dcuccia/digital-handbell/docs/measurements/2026-09-27-router-bakeoff/quilter-inferred/bypass_capacitors.csv

capacitor | bypassed_component | bypassed_pin | capacitance
C5 | U1 | 8 | 100
C9 | U2 | 5 | 100
C10 | U2 | 5 | 100
C11 | U2 | 5 | 100
C12 | U2 | 5 | 100
C13 | U2 | 5 | 100
C14 | U2 | 5 | 100
C15 | U2 | 5 | 100
C17 | U2 | 5 | 100
C23 | U2 | 5 | 100
C24 | U2 | 5 | 100
C26 | U5 | 3 | 22000
C27 | U4 | 7 | 22000
C28 | U4 | 8 | 22000
C2 | IC1 | 20 | 0.015
C3 | R6 | 1 | 0.015
C4 | U2 | 5 | 100
C6 | IC1 | 23 | 100
C7 | IC1 | 45 | 100
C8 | IC1 | 50 | 100
C21 | FB2 | 2 | 0.22
C22 | FB1 | 2 | 0.22
C1 | U2 | 1 | 100
C16 | U4 | 7 | 100
C18 | IC1 | 23 | 100
C19 | U4 | 7 | 100
C20 | CHG_EN0 | 2 | 100
C25 | IC1 | 30 | 10
