dcuccia/digital-handbell/hardware/handbell/iterations/printed-bell-front/reports/footprint-movements.csv

reference | from_native_xy_angle | to_native_xy_angle | from_side | to_side
C1 | [-5.819979, -12.535118, 180.0] | [-4.034775, -13.791182, 90] | F | F
C2 | [-7.491404, -0.208214, 90.0] | [-9.0964, -3.04755, 90] | F | F
C3 | [-7.491346, 1.914027, 270.0] | [-9.100819, -0.800669, 270] | F | F
C4 | [-13.404896, -5.309687, 0.0] | [-15.993581, -9.414015, 0] | F | F
C5 | [-11.417907, -10.812876, 180.0] | [-16.178591, -2.508548, 0] | F | F
C6 | [8.689622, -0.182451, 180.0] | [5.497898, -0.400256, 180] | F | F
C7 | [8.460429, 2.217699, 180.0] | [7.803336, 2.200014, 180] | F | F
C8 | [8.463329, 3.418004, 0.0] | [5.501069, 2.200145, 0] | F | F
C9 | [-5.765769, 3.036206, 180.0] | [2.615534, -5.271328, 90] | F | F
C10 | [3.059734, -7.563574, 180.0] | [5.294511, -6.217731, 90] | F | F
C11 | [-7.169298, 6.97243, 90.0] | [-0.994073, 5.195623, 270] | F | F
C12 | [3.059361, -6.228689, 180.0] | [-0.99995, -5.269923, 90] | F | F
C13 | [7.694268, 4.618099, 0.0] | [5.502546, 3.500537, 0] | F | F
C14 | [-2.832032, 1.442344, 180.0] | [-5.195705, 2.304504, 180] | F | F
C15 | [-2.408704, -1.416949, 90.0] | [2.589143, 5.196168, 270] | F | F
C16 | [10.584754, -15.261328, 0.0] | [11.33959, -6.983099, 0] | B | F
C17 | [8.390974, 1.017594, 0.0] | [5.499429, 0.897675, 0] | F | F
C18 | [-2.833131, 2.644313, 0.0] | [-5.19636, 1.003449, 0] | F | F
C19 | [7.434754, -15.811328, 0.0] | [14.218731, -6.93737, 0] | B | F
C20 | [-2.310305, 15.995891, 270.0] | [4.846036, -16.283889, 90] | F | F
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
U4 | [10.105463, -12.411328, 0.0] | [10.725323, -10.087789, 0] | B | F
U5 | [-1.168351, 15.064739, 90.0] | [-4.198999, 16.001796, 0] | B | F
U6 | [-11.496466, 7.350217, 0.0] | [-11.502673, 7.349061, 0] | F | F
Y1 | [-5.391298, 0.68593, 90.0] | [-6.925199, -1.997404, 90] | F | F
