dcuccia/digital-handbell/mechanical/studies/2026-09-13-printed-bell/imu-four-layer-review/extended-run/INERT-flush-carrier.stl

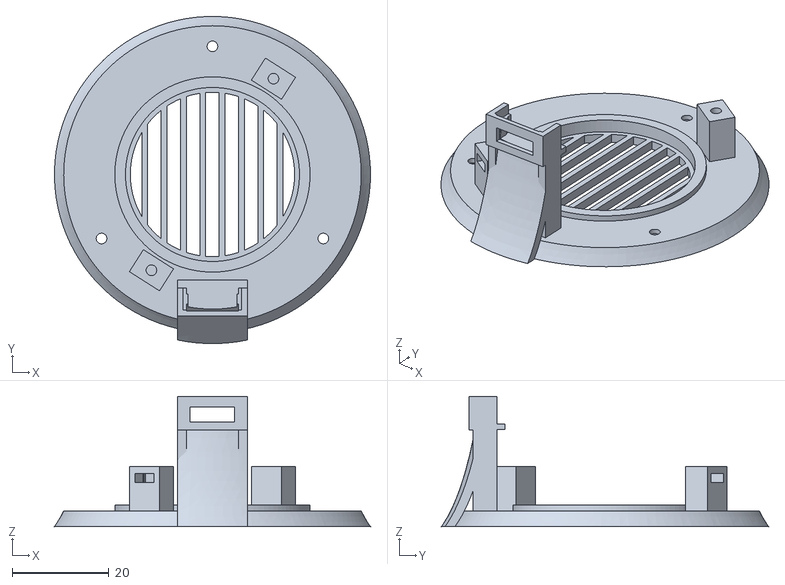
[picture p21: CAD file, 2026-09-24]
mechanical/studies/2026-09-13-printed-bell/imu-four-layer-review/extended-run/INERT-flush-carrier.stl
65.4 x 67.7 x 27.0
