dcuccia/digital-handbell/mechanical/grille.stl

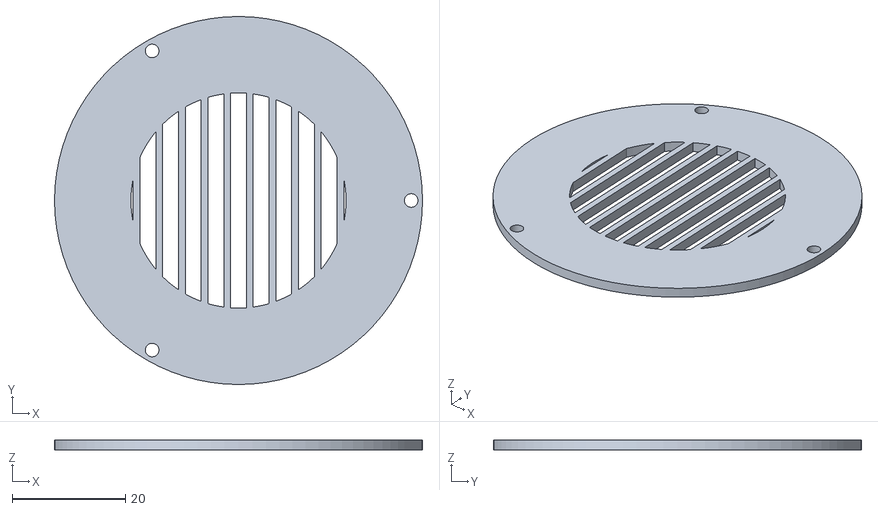
[picture p22: CAD file, 2026-09-07]
mechanical/grille.stl
65.0 x 65.0 x 1.80
