dcuccia/digital-handbell/mechanical/studies/2026-09-09-measured-speaker/outward-body-screen.step

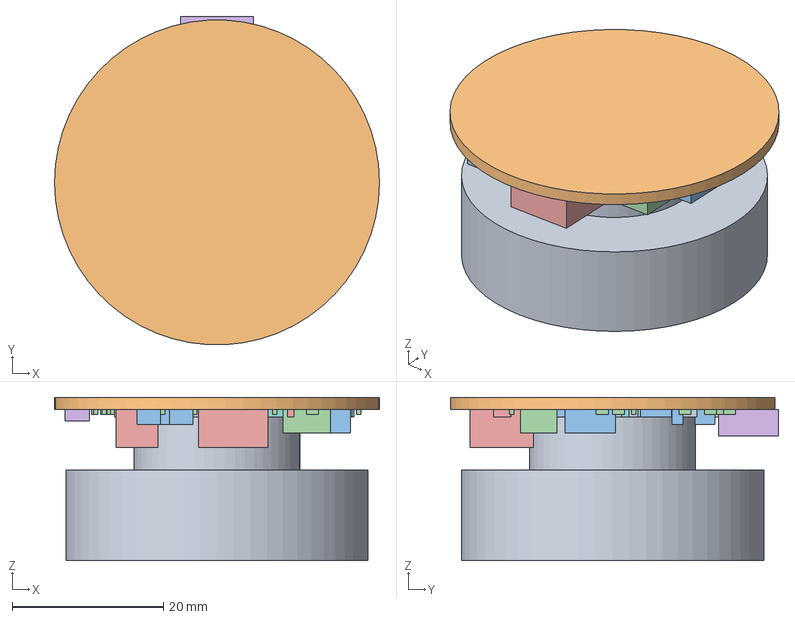
[picture p23: CAD file, 2026-09-09]
mechanical/studies/2026-09-09-measured-speaker/outward-body-screen.step
43.0 x 43.4 x 21.6 mm
