dcuccia/digital-handbell/mechanical/studies/2026-09-11-t8-cartridge/alternatives/baseline-fixed-stack/populated-t8-pcba-without-contacts.step

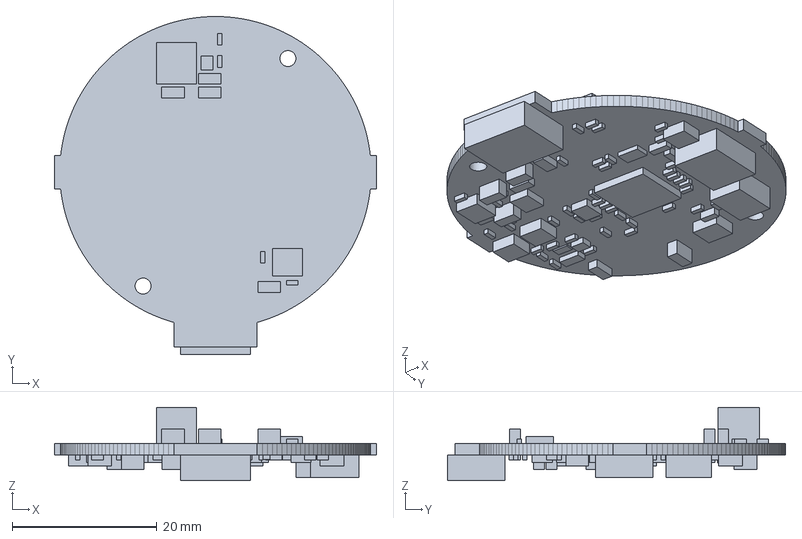
[picture p24: CAD file, 2026-09-12]
mechanical/studies/2026-09-11-t8-cartridge/alternatives/baseline-fixed-stack/populated-t8-pcba-without-contacts.step
44.5 x 46.6 x 10.1 mm
