dcuccia/digital-handbell/mechanical/speaker-envelope-maximum.stl

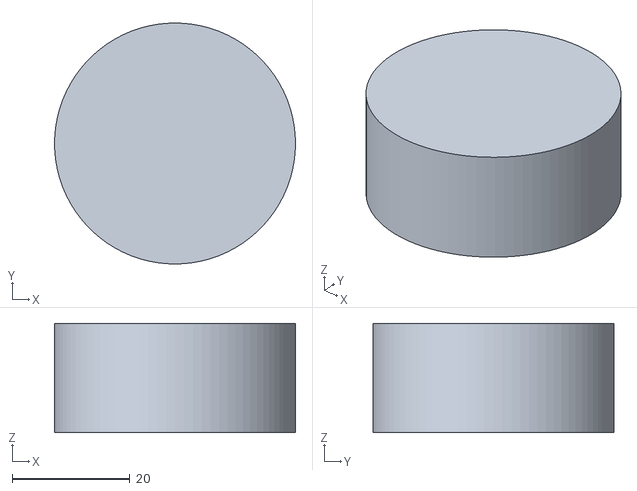
[picture p26: CAD file, 2026-09-07]
mechanical/speaker-envelope-maximum.stl
40.9 x 40.9 x 18.5
