dcuccia/digital-handbell/mechanical/studies/2026-09-09-integrated-cartridge/INERT-integrated-grille-seat-body.stl

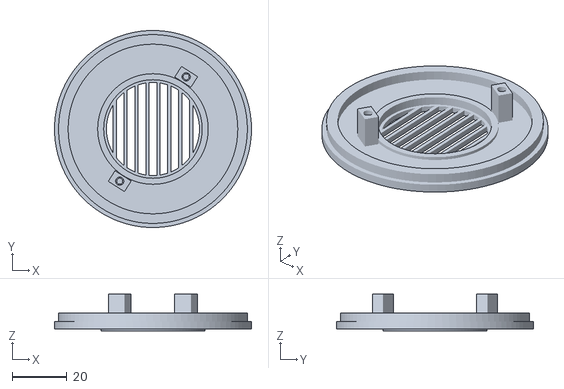
[picture p27: CAD file, 2026-09-10]
mechanical/studies/2026-09-09-integrated-cartridge/INERT-integrated-grille-seat-body.stl
72.0 x 72.0 x 13.5
