dcuccia/digital-handbell/mechanical/studies/2026-09-09-measured-speaker/measured-speaker-study.FCStd

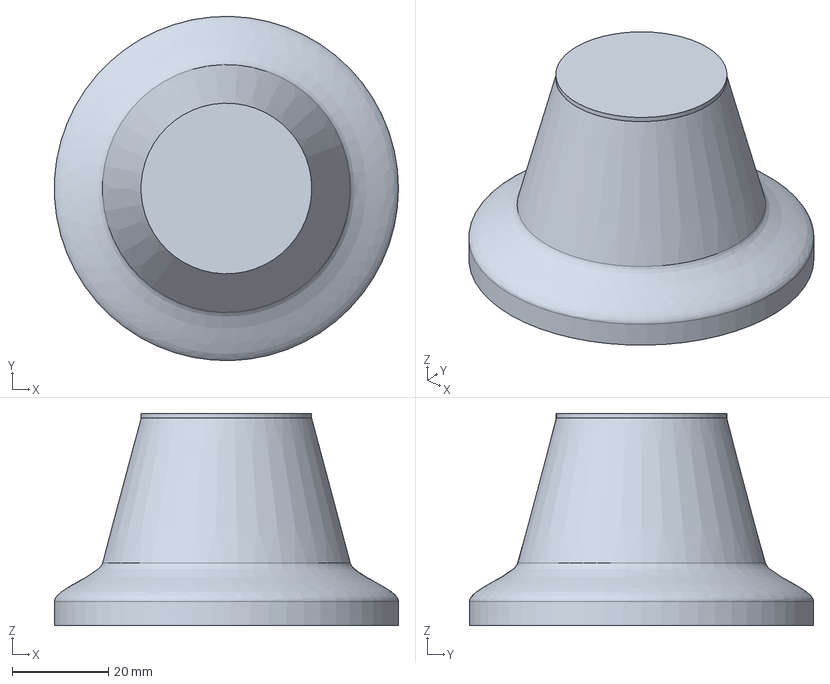
[picture p28: CAD file, 2026-09-09]
mechanical/studies/2026-09-09-measured-speaker/measured-speaker-study.FCStd
71.3 x 71.4 x 44.0 mm
ASSUMED shell; no USB slot; hide to inspect
ILLUSTRATIVE: straight basket interpolation
SCREEN: full measured D40 x H19 body cylinder
SCREEN: full-width basket + measured magnet
Unrouted substrate at z20
C1 - original unscaled component proxy
C2 - original unscaled component proxy
C3 - original unscaled component proxy
C4 - original unscaled component proxy
C5 - original unscaled component proxy
C6 - original unscaled component proxy
C7 - original unscaled component proxy
C8 - original unscaled component proxy
C9 - original unscaled component proxy
C10 - original unscaled component proxy
C11 - original unscaled component proxy
C12 - original unscaled component proxy
C13 - original unscaled component proxy
C14 - original unscaled component proxy
C15 - original unscaled component proxy
C16 - original unscaled component proxy
C17 - original unscaled component proxy
C18 - original unscaled component proxy
C19 - original unscaled component proxy
C20 - original unscaled component proxy
C21 - original unscaled component proxy
C22 - original unscaled component proxy
C23 - original unscaled component proxy
C24 - original unscaled component proxy
C25 - original unscaled component proxy
C26 - original unscaled component proxy
C27 - original unscaled component proxy
C28 - original unscaled component proxy
CHG0 - original unscaled component proxy
D3 - original unscaled component proxy
D4 - original unscaled component proxy
FB1 - original unscaled component proxy
FB2 - original unscaled component proxy
IC1 - original unscaled component proxy
IC4 - original unscaled component proxy
J1 - original unscaled component proxy
J2 - original unscaled component proxy
L0 - original unscaled component proxy
L1 - original unscaled component proxy
Q1 - original unscaled component proxy
Q2 - original unscaled component proxy
Q3 - original unscaled component proxy
Q4 - original unscaled component proxy
R1 - original unscaled component proxy
R2 - original unscaled component proxy
R3 - original unscaled component proxy
R4 - original unscaled component proxy
R5 - original unscaled component proxy
R6 - original unscaled component proxy
R7 - original unscaled component proxy
R8 - original unscaled component proxy
R9 - original unscaled component proxy
R10 - original unscaled component proxy
R11 - original unscaled component proxy
R12 - original unscaled component proxy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
