dcuccia/digital-handbell/mechanical/populated-pcba-proxy.step

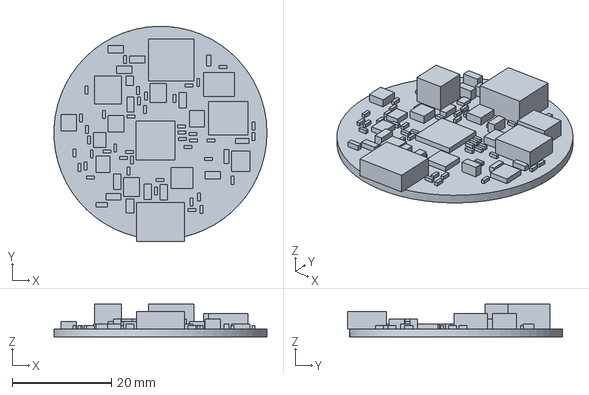
[picture p29: CAD file, 2026-09-07]
mechanical/populated-pcba-proxy.step
43.0 x 43.5 x 6.60 mm
