dcuccia/digital-handbell/mechanical/studies/2026-09-11-t8-cartridge/alternatives/baseline-fixed-stack/battery-cover.step

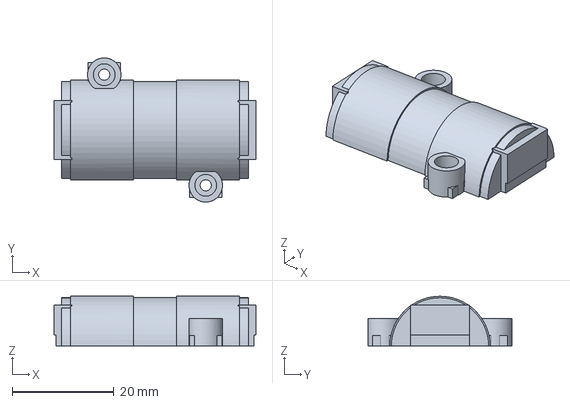
[picture p30: CAD file, 2026-09-12]
mechanical/studies/2026-09-11-t8-cartridge/alternatives/baseline-fixed-stack/battery-cover.step
39.8 x 28.4 x 9.78 mm
