dcuccia/digital-handbell/mechanical/studies/2026-09-11-t8-cartridge/INERT-battery-cradle.stl

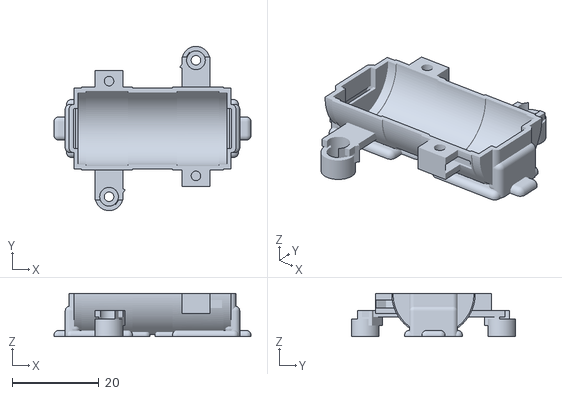
[picture p31: CAD file, 2026-09-12]
mechanical/studies/2026-09-11-t8-cartridge/INERT-battery-cradle.stl
45.3 x 37.8 x 9.90
