dcuccia/digital-handbell/mechanical/speaker-envelope-nominal.stl

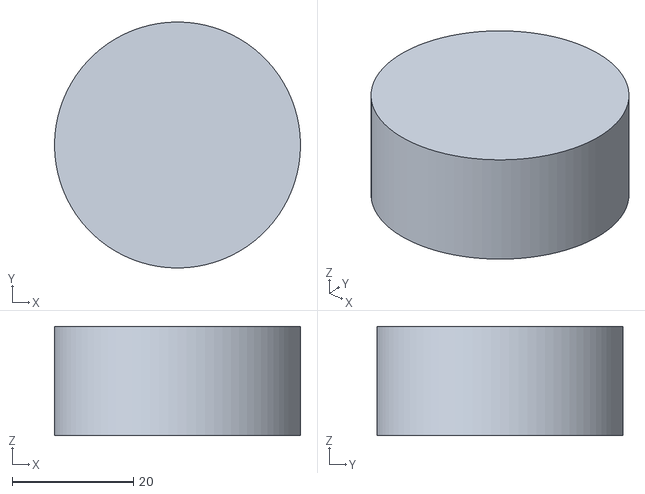
[picture p32: CAD file, 2026-09-07]
mechanical/speaker-envelope-nominal.stl
40.5 x 40.5 x 18.0
