dcuccia/digital-handbell/mechanical/studies/2026-09-09-integrated-cartridge/integrated-cartridge-draft.FCStd

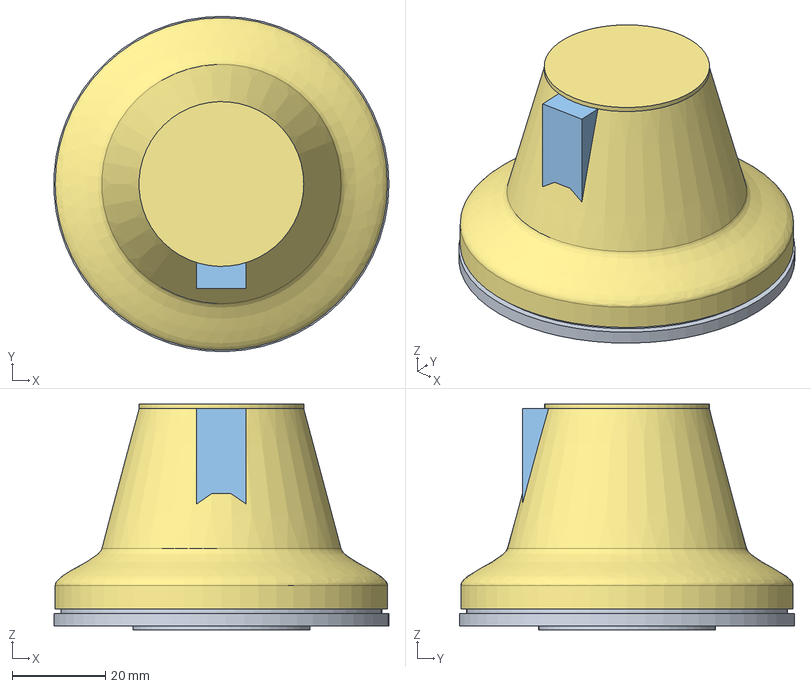
[picture p33: CAD file, 2026-09-10]
mechanical/studies/2026-09-09-integrated-cartridge/integrated-cartridge-draft.FCStd
71.9 x 72.0 x 48.5 mm
IntegratedGrilleSeatBody
RemovableCaptureYoke
MeasuredSpeakerBodyScreen
PopulatedWingPCBA
YokeScrew1 - ordinary M2 placeholder, not selected hardware
LowerInsert1 - ordinary M2 placeholder, not selected hardware
YokeScrew2 - ordinary M2 placeholder, not selected hardware
LowerInsert2 - ordinary M2 placeholder, not selected hardware
MH1Screw - ordinary M2 placeholder, not selected hardware
MH1Washer - ordinary M2 placeholder, not selected hardware
MH1Insert - ordinary M2 placeholder, not selected hardware
MH2Screw - ordinary M2 placeholder, not selected hardware
MH2Washer - ordinary M2 placeholder, not selected hardware
MH2Insert - ordinary M2 placeholder, not selected hardware
ASSUMED shell; required USB cutout not subtracted
ILLUSTRATIVE straight basket; not the collision screen
SubstrateWithTwoDrills
C1 F
C2 F
C3 F
C4 F
C5 F
C6 F
C7 F
C8 F
C9 F
C10 F
C11 F
C12 F
C13 F
C14 F
C15 F
C16 B
C17 F
C18 F
C19 B
C20 F
C21 F
C22 F
C23 F
C24 F
C25 F
C26 B
C27 B
C28 B
CHG0 F
D3 F
D4 F
FB1 F
FB2 F
IC1 F
IC4 F
J1 F
J2 F
L0 F
L1 B
Q1 F
Q2 F
Q3 F
Q4 F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
