dcuccia/digital-handbell/mechanical/studies/2026-09-09-measured-speaker/speaker-interpolated-stations.step

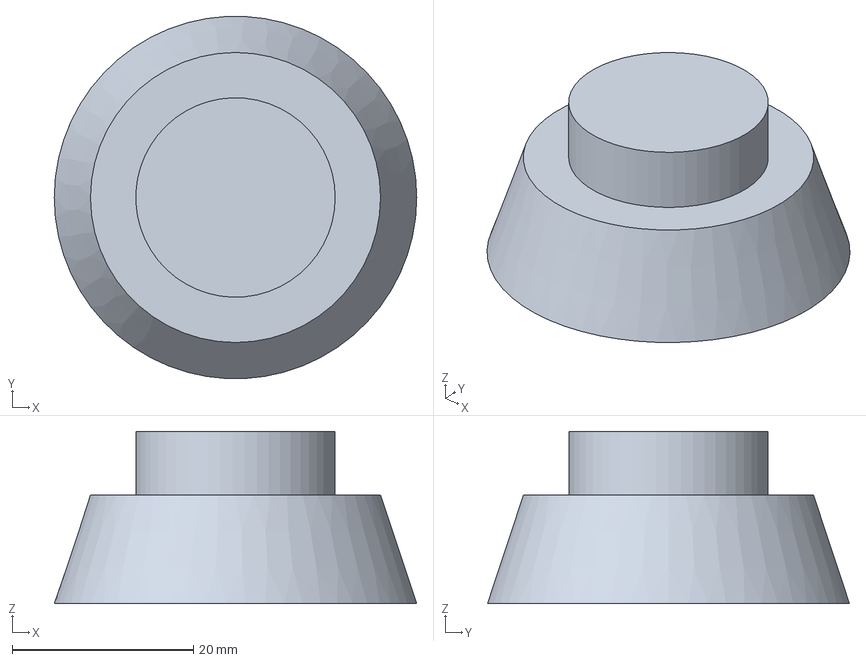
[picture p34: CAD file, 2026-09-09]
mechanical/studies/2026-09-09-measured-speaker/speaker-interpolated-stations.step
40.0 x 39.9 x 19.0 mm
