dcuccia/digital-handbell/mechanical/studies/2026-09-11-t8-cartridge/alternatives/baseline-fixed-stack/populated-t8-pcba.step

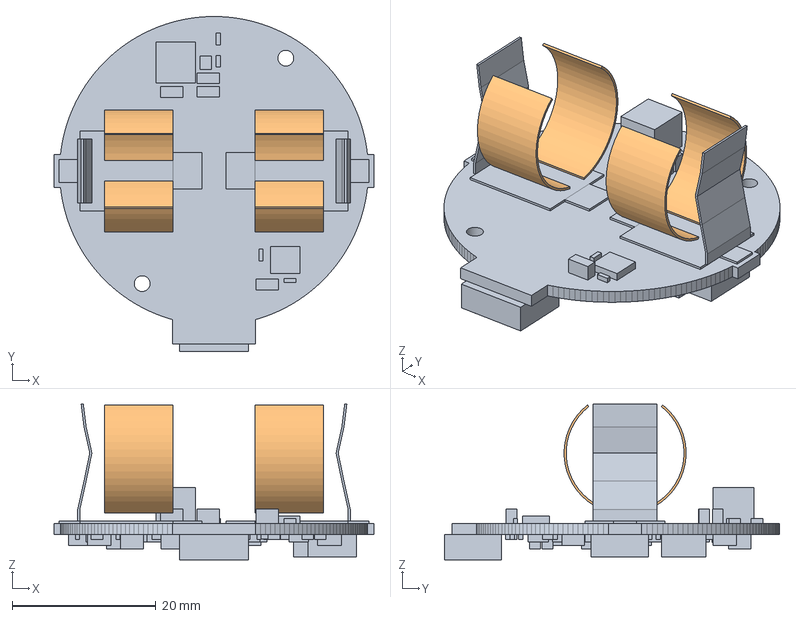
[picture p35: CAD file, 2026-09-12]
mechanical/studies/2026-09-11-t8-cartridge/alternatives/baseline-fixed-stack/populated-t8-pcba.step
44.5 x 46.6 x 21.7 mm
