dcuccia/digital-handbell/mechanical/battery-dummy-compact.stl

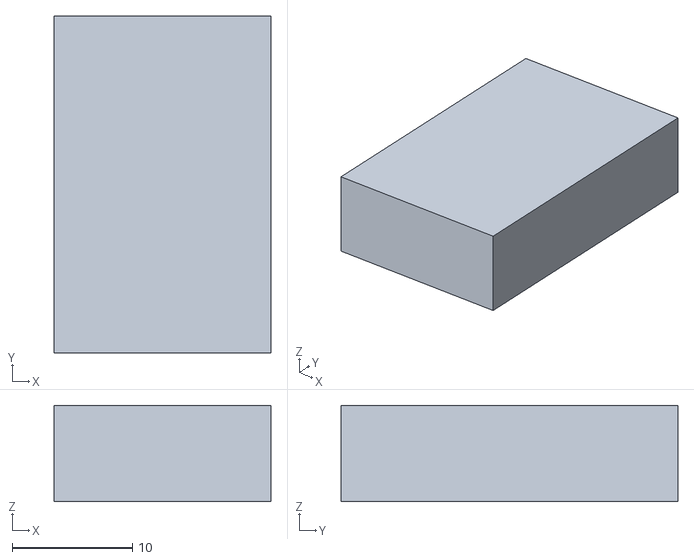
[picture p36: CAD file, 2026-09-07]
mechanical/battery-dummy-compact.stl
18.0 x 28.0 x 8.00
