dcuccia/digital-handbell/mechanical/studies/2026-09-09-integrated-cartridge/INERT-removable-capture-yoke.stl

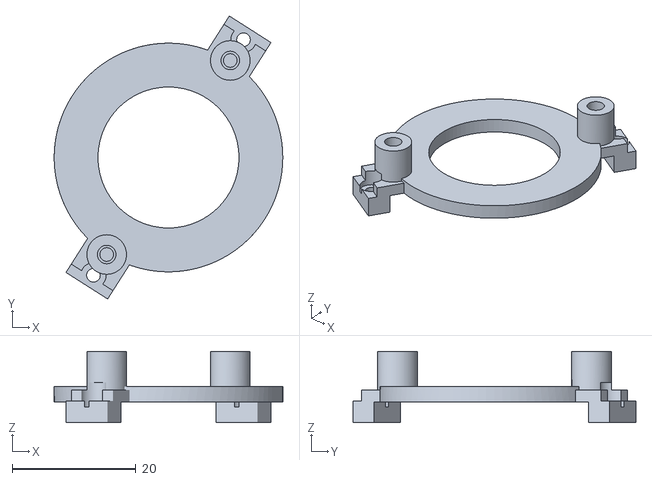
[picture p37: CAD file, 2026-09-10]
mechanical/studies/2026-09-09-integrated-cartridge/INERT-removable-capture-yoke.stl
37.0 x 45.8 x 11.5
