dcuccia/digital-handbell/mechanical/studies/2026-09-11-t8-cartridge/alternatives/baseline-fixed-stack/battery-cradle.step

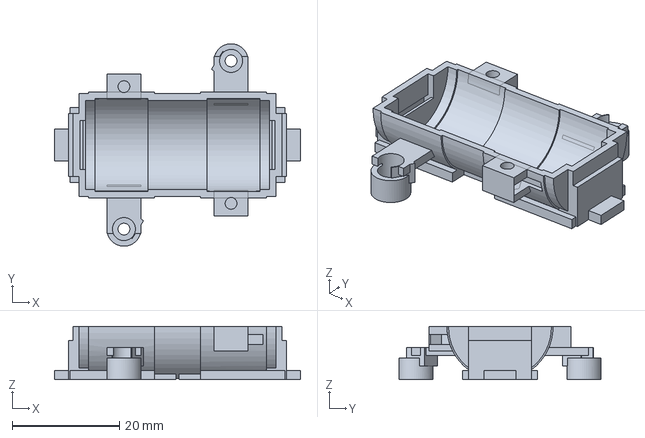
[picture p38: CAD file, 2026-09-12]
mechanical/studies/2026-09-11-t8-cartridge/alternatives/baseline-fixed-stack/battery-cradle.step
45.9 x 37.8 x 9.90 mm
