dcuccia/digital-handbell/mechanical/speaker-illustrative-unmeasured.step

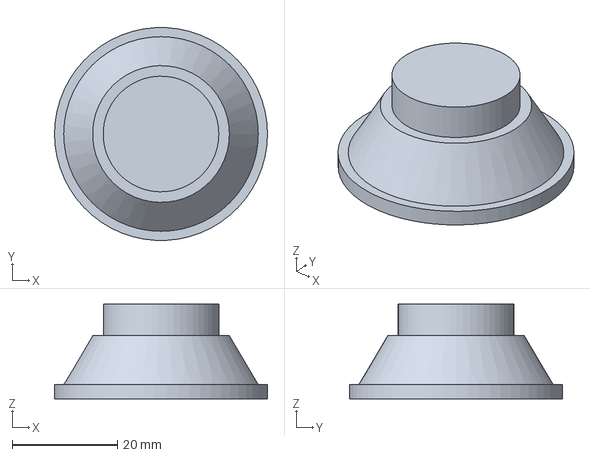
[picture p39: CAD file, 2026-09-07]
mechanical/speaker-illustrative-unmeasured.step
40.5 x 40.4 x 18.0 mm
