dcuccia/digital-handbell/mechanical/studies/2026-09-11-t8-cartridge/alternatives/baseline-fixed-stack/t8-cartridge.FCStd

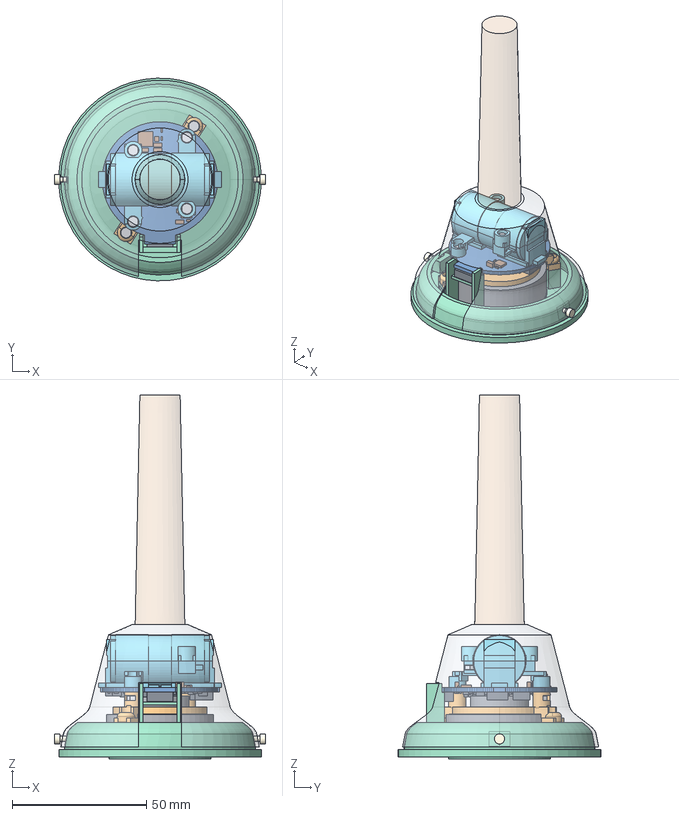
[picture p40: CAD file, 2026-09-12]
mechanical/studies/2026-09-11-t8-cartridge/alternatives/baseline-fixed-stack/t8-cartridge.FCStd
78.6 x 75.5 x 135.6 mm
WorkingShellWithProposedOpenSlot
HandleExteriorOnly
FrontBodyGrilleRegisterUSBBezel
RemovableSpeakerCaptureYoke
SpeakerConditionalBodyScreen
PCBSubstrateExactInterface
T8FullUnclippedCellCanEnvelope
LoadBearingInsulatingBatteryCradle
RemovableBatteryCaptureCover
Component_C1
Component_C2
Component_C3
Component_C4
Component_C5
Component_C6
Component_C7
Component_C8
Component_C9
Component_C10
Component_C11
Component_C12
Component_C13
Component_C14
Component_C15
Component_C16
Component_C17
Component_C18
Component_C19
Component_C20
Component_C21
Component_C22
Component_C23
Component_C24
Component_C25
Component_C26
Component_C27
Component_C28
Component_C30
Component_CHG0
Component_D3
Component_D4
Component_FB1
Component_FB2
Component_IC1
Component_IC4
Component_J1
Component_J2
Component_L0
Component_L1
Component_Q1
Component_Q2
Component_Q3
Component_Q4
Component_Q5
Component_R1
Component_R2
Component_R3
Component_R4
Component_R5
Component_R6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
