dcuccia/digital-handbell/mechanical/battery-dummy-primary.stl

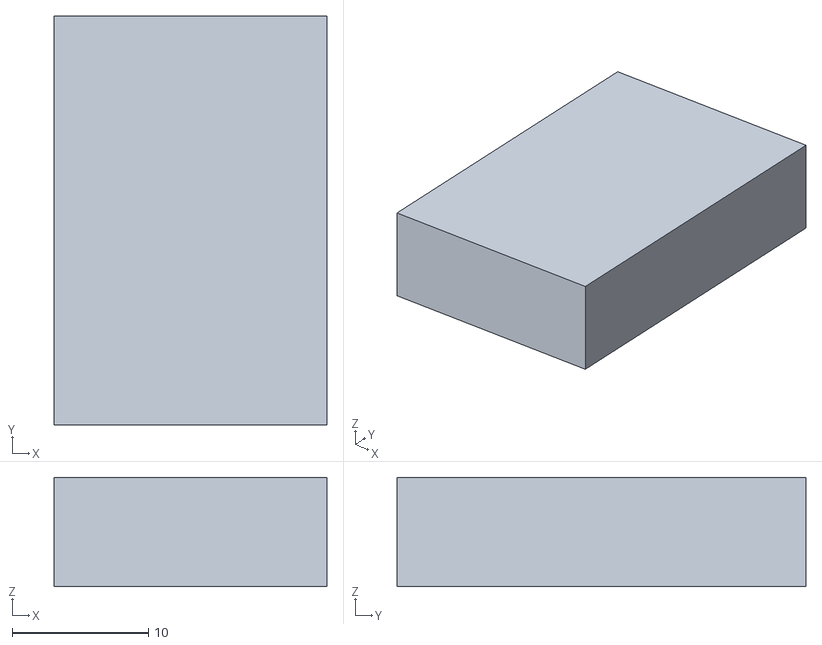
[picture p41: CAD file, 2026-09-07]
mechanical/battery-dummy-primary.stl
20.0 x 30.0 x 8.00
