dcuccia/digital-handbell/mechanical/studies/2026-09-11-t8-cartridge/battery-cover.step

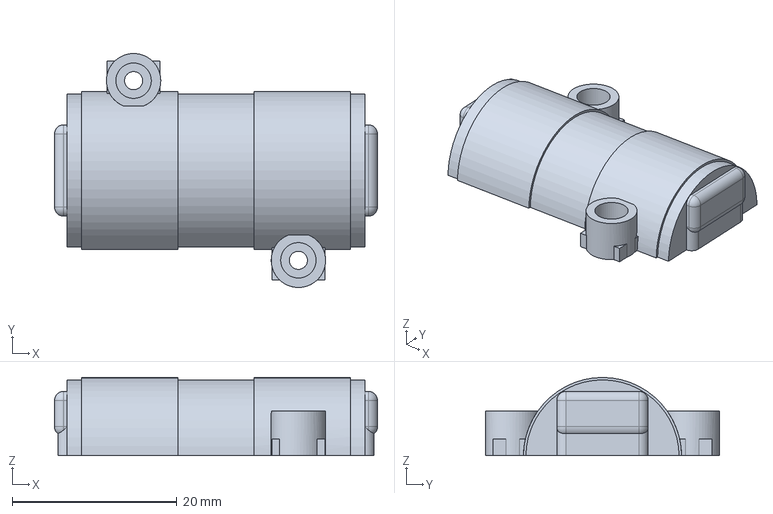
[picture p42: CAD file, 2026-09-12]
mechanical/studies/2026-09-11-t8-cartridge/battery-cover.step
39.2 x 28.4 x 9.48 mm
