dcuccia/digital-handbell/mechanical/studies/2026-09-13-printed-bell/imu-four-layer-review/extended-run/cell-cover.step

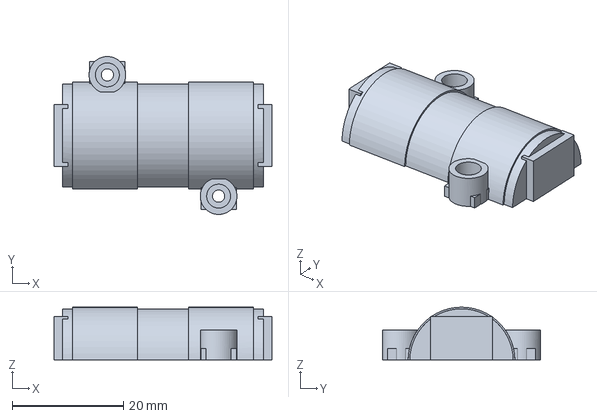
[picture p43: CAD file, 2026-09-24]
mechanical/studies/2026-09-13-printed-bell/imu-four-layer-review/extended-run/cell-cover.step
39.2 x 28.4 x 9.48 mm
