dcuccia/digital-handbell/mechanical/studies/2026-09-13-printed-bell/imu-four-layer-review/extended-run/black-handle.step

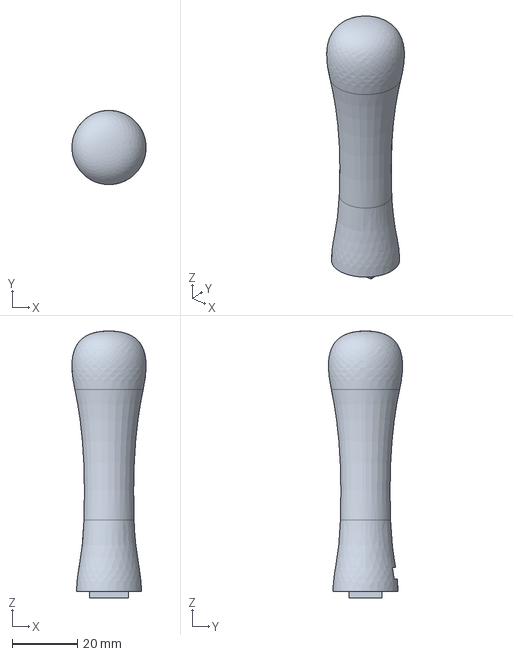
[picture p44: CAD file, 2026-09-24]
mechanical/studies/2026-09-13-printed-bell/imu-four-layer-review/extended-run/black-handle.step
22.8 x 22.8 x 82.0 mm
