dcuccia/digital-handbell/mechanical/battery-clearance-primary.stl

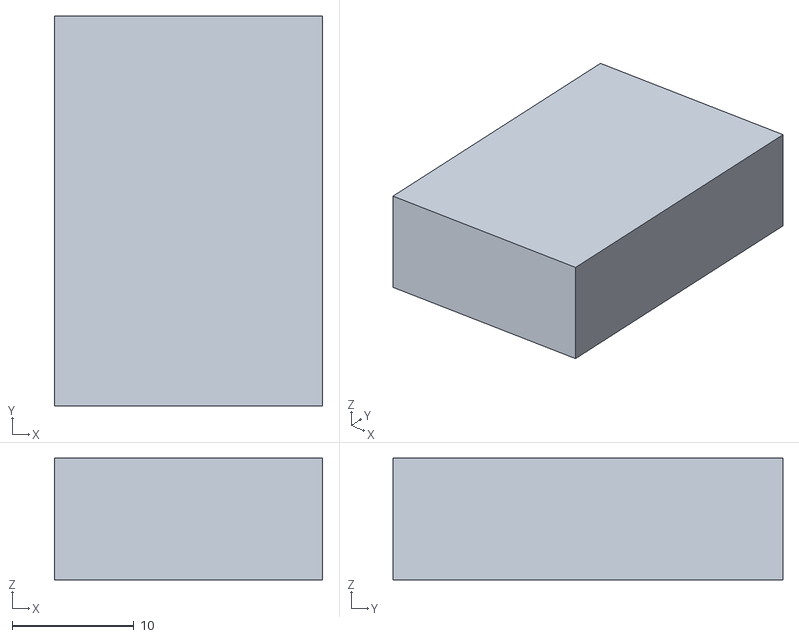
[picture p45: CAD file, 2026-09-07]
mechanical/battery-clearance-primary.stl
22.0 x 32.0 x 10.0
