dcuccia/digital-handbell/mechanical/studies/2026-09-13-printed-bell/imu-four-layer-review/extended-run/INERT-pcba-without-contacts.step

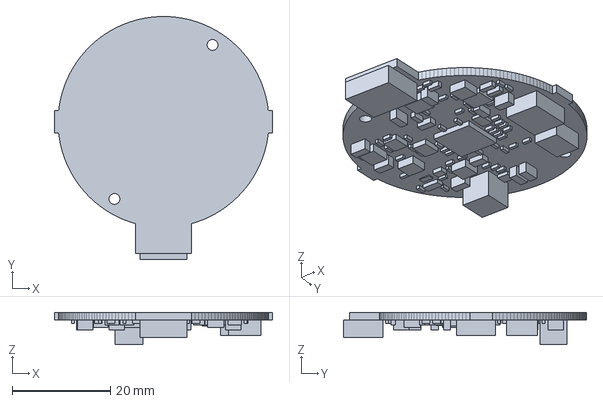
[picture p46: CAD file, 2026-09-24]
mechanical/studies/2026-09-13-printed-bell/imu-four-layer-review/extended-run/INERT-pcba-without-contacts.step
44.5 x 49.5 x 6.60 mm
