dcuccia/digital-handbell/mechanical/fit-carrier.stl

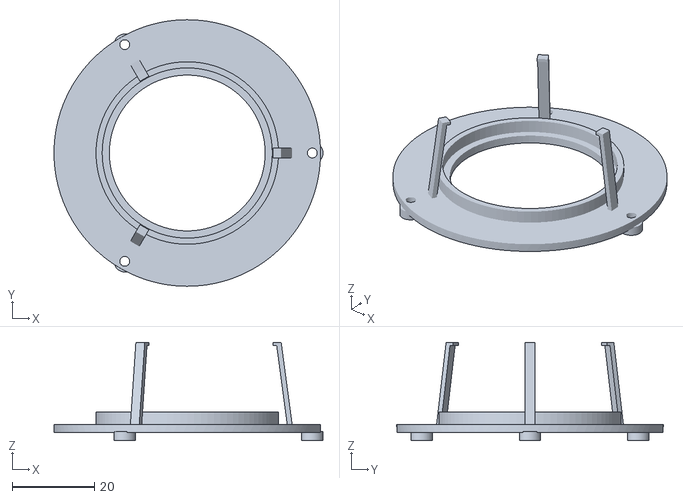
[picture p47: CAD file, 2026-09-07]
mechanical/fit-carrier.stl
65.6 x 65.0 x 24.0
