dcuccia/digital-handbell/mechanical/studies/2026-09-11-t8-cartridge/populated-t8-pcba.step

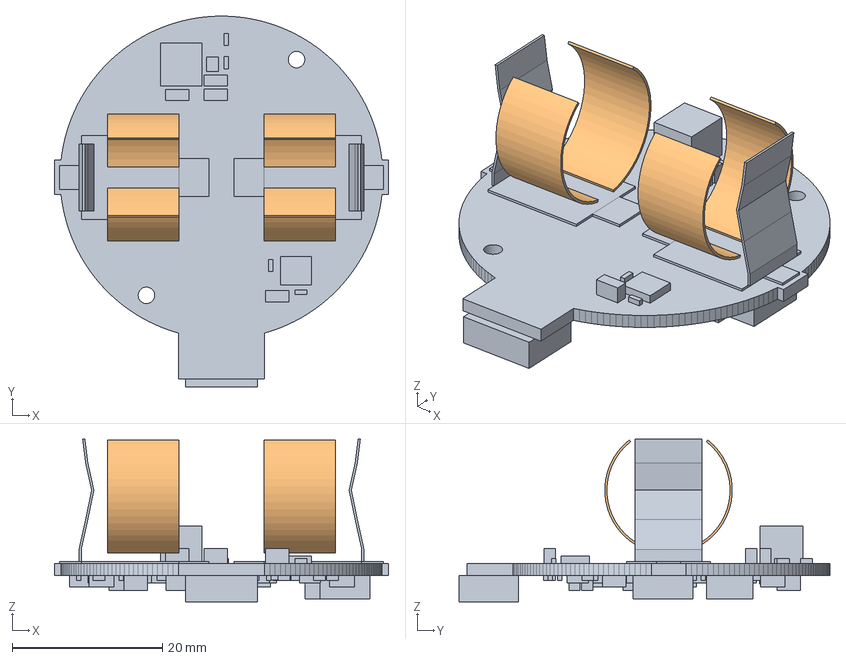
[picture p48: CAD file, 2026-09-12]
mechanical/studies/2026-09-11-t8-cartridge/populated-t8-pcba.step
44.5 x 49.4 x 21.7 mm
