dcuccia/digital-handbell/mechanical/battery-clearance-compact.stl

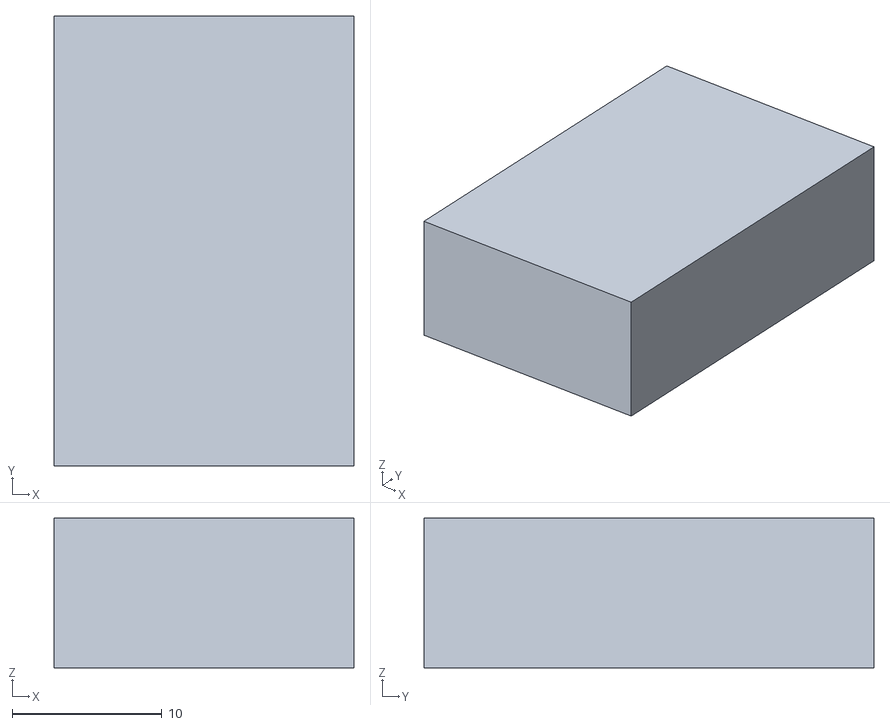
[picture p49: CAD file, 2026-09-07]
mechanical/battery-clearance-compact.stl
20.0 x 30.0 x 10.0
