dcuccia/digital-handbell/mechanical/handbell-feasibility.FCStd

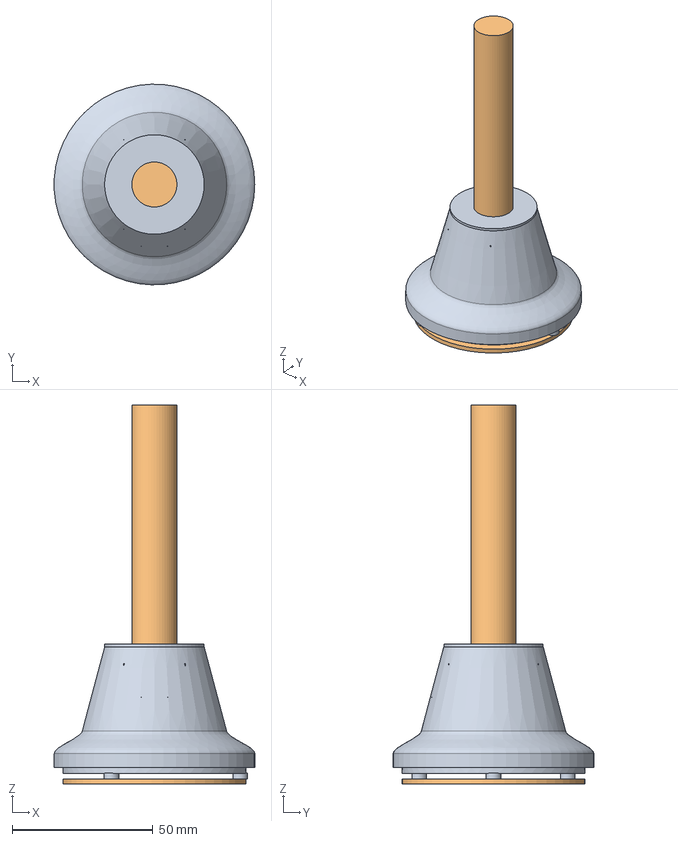
[picture p50: CAD file, 2026-09-07]
mechanical/handbell-feasibility.FCStd
71.3 x 71.4 x 134.8 mm
Bell shell - assumed inner profile / placeholder wall
Handle EXTERIOR ONLY - no usable interior assumed
EK1794 full 40.9 x 18.5 max envelope PROXY
INERT battery-sized block - NOT a selected pack
PCB physical substrate (not a routed board)
C1 - approximate component PROXY
C2 - approximate component PROXY
C3 - approximate component PROXY
C4 - approximate component PROXY
C5 - approximate component PROXY
C6 - approximate component PROXY
C7 - approximate component PROXY
C8 - approximate component PROXY
C9 - approximate component PROXY
C10 - approximate component PROXY
C11 - approximate component PROXY
C12 - approximate component PROXY
C13 - approximate component PROXY
C14 - approximate component PROXY
C15 - approximate component PROXY
C16 - approximate component PROXY
C17 - approximate component PROXY
C18 - approximate component PROXY
C19 - approximate component PROXY
C20 - approximate component PROXY
C21 - approximate component PROXY
C22 - approximate component PROXY
C23 - approximate component PROXY
C24 - approximate component PROXY
C25 - approximate component PROXY
C26 - approximate component PROXY
C27 - approximate component PROXY
C28 - approximate component PROXY
CHG0 - approximate component PROXY
D3 - approximate component PROXY
D4 - approximate component PROXY
FB1 - approximate component PROXY
FB2 - approximate component PROXY
IC1 - approximate component PROXY
IC4 - approximate component PROXY
J1 - approximate component PROXY
J2 - approximate component PROXY
L0 - approximate component PROXY
L1 - approximate component PROXY
Q1 - approximate component PROXY
Q2 - approximate component PROXY
Q3 - approximate component PROXY
Q4 - approximate component PROXY
R1 - approximate component PROXY
R2 - approximate component PROXY
R3 - approximate component PROXY
R4 - approximate component PROXY
R5 - approximate component PROXY
R6 - approximate component PROXY
R7 - approximate component PROXY
R8 - approximate component PROXY
R9 - approximate component PROXY
R10 - approximate component PROXY
R11 - approximate component PROXY
R12 - approximate component PROXY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
