dcuccia/digital-handbell/mechanical/studies/2026-09-13-printed-bell/imu-four-layer-review/extended-run/shell.step

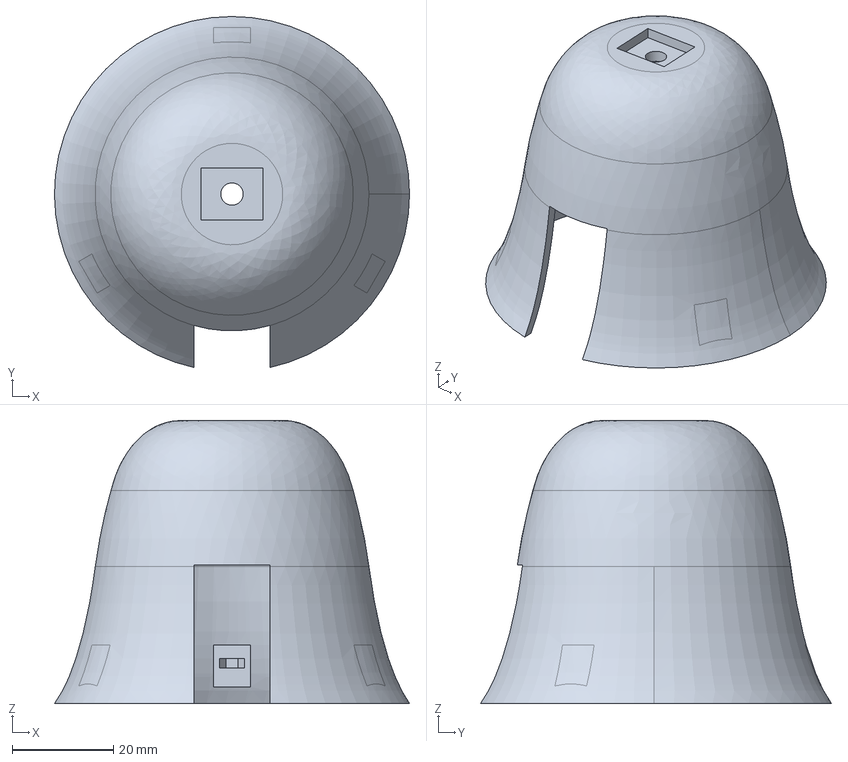
[picture p51: CAD file, 2026-09-24]
mechanical/studies/2026-09-13-printed-bell/imu-four-layer-review/extended-run/shell.step
70.0 x 69.2 x 55.8 mm
