dcuccia/digital-handbell/mechanical/studies/2026-09-11-t8-cartridge/INERT-body.stl

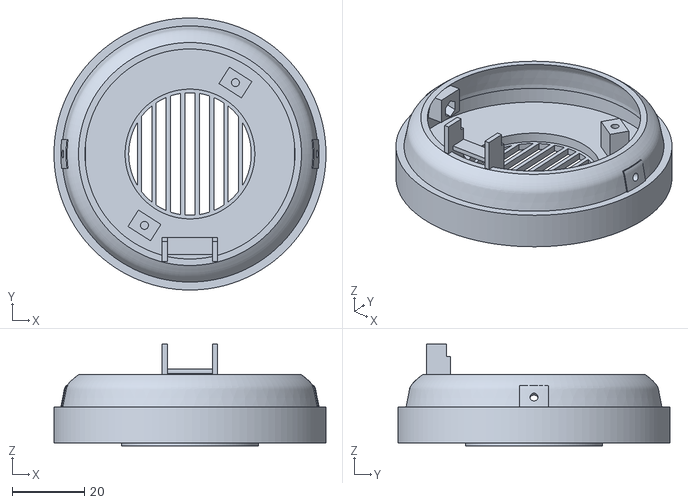
[picture p53: CAD file, 2026-09-12]
mechanical/studies/2026-09-11-t8-cartridge/INERT-body.stl
75.5 x 75.5 x 28.2
