dcuccia/digital-handbell/mechanical/studies/2026-09-13-printed-bell/imu-four-layer-review/extended-run/removable-cartridge.step

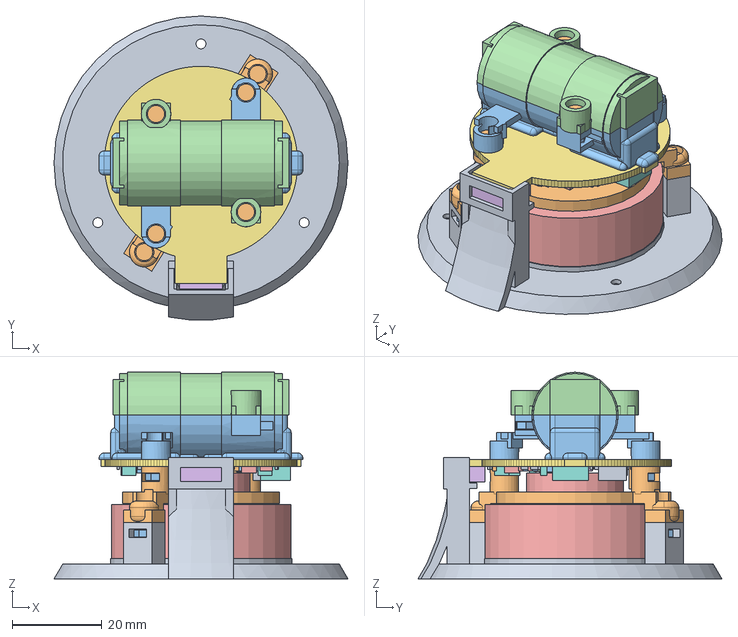
[picture p54: CAD file, 2026-09-24]
mechanical/studies/2026-09-13-printed-bell/imu-four-layer-review/extended-run/removable-cartridge.step
65.4 x 67.6 x 46.0 mm
