dcuccia/digital-handbell/mechanical/studies/2026-09-13-printed-bell/views/grille.png

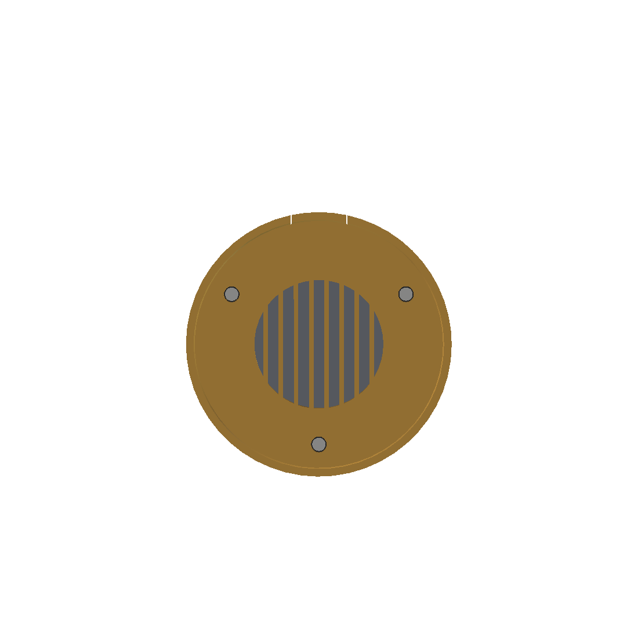
mechanical/studies/2026-09-13-printed-bell/views/grille.png
