dcuccia/digital-handbell/docs/measurements/2026-09-27-router-bakeoff/quilter-inferred/ground_nets.csv

net_name | is_primary | use_region_pour
GND | true | false
/PROT_FET_RETURN | false | false
