dcuccia/digital-handbell/docs/measurements/2026-09-27-router-bakeoff/quilter-inferred/high_current_nets.csv

net_name | max_current | use_power_pour
+3V3 | 500 | true
GND | 500 | true
VAMP | 500 | true
VBAT | 500 | true
VBUS | 500 | true
VCORE | 500 | true
VHI | 500 | true
