dcuccia/digital-handbell/docs/measurements/2026-09-27-router-bakeoff/quilter-inferred/differential_pairs.csv

positive_net_name | negative_net_name | differential_impedance | single_ended_impedance | frequency
D+ | D- | 100 |  | 1
USB_D+ | USB_D- | 100 |  | 1
VO+ | VO- | 100 |  | 1
