dcuccia/digital-handbell/hardware/handbell/iterations/printed-bell-front/reports/back-native.pdf

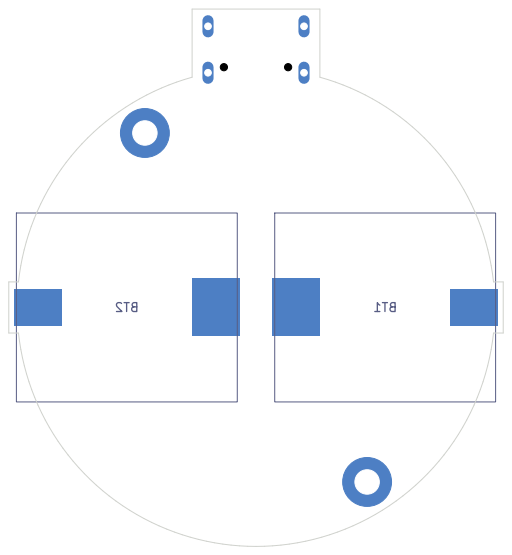
[picture p64: page 1]
