dcuccia/digital-handbell/tools/experiments/route_core_distribution.py

# SPDX-License-Identifier: MIT
"""Bounded VCORE candidate using the existing search with native obstacle masks."""
import argparse
import json
import math
import os
from pathlib import Path
import shutil
import sys
import time
import uuid

import numpy as np

sys.path.insert(0, str(Path(__file__).resolve().parents[1]))
from check_front_ground import board_polygon, bounds_polygon
from kicad_sexpr import apply_edits, load
from route_clock_local import PACKAGE, sha
from route_printed_bell import GRID, Router

BASE = "57ae2c0b54e1313fb175ccdecdee07ebda07abed5151e776c9767511135d440f"
PAIRS = (("C6.2", "C7.2"),)
STAGE = "core-distribution-right"
INPUT_COMMIT = "60db9b4"
ROUTING_BOUNDS = (-12, -10, 12, 10)
SEARCH_MARGIN = 4
SEARCH_LIMIT = 80000
TARGET_ANCHORS = {}
REMOVED_TRACK_UUIDS = ()
FRONT_ONLY = False


class NativeRouter(Router):
    def __init__(self, board, pcb):
        self.pcb = pcb
        self.tracks, self.vias, self.results = [], [], []
        self.obstacles = [p for f in board.GetFootprints() for p in f.Pads()] + list(board.GetTracks())
        self.metal = []
        manifest = json.loads((PACKAGE / "placement-manifest.json").read_text(encoding="utf-8"))
        self.boundary = board_polygon(pcb, manifest, .55)
        contact = json.loads((PACKAGE / "battery-contact-interface.json").read_text(encoding="utf-8"))
        primitives = contact["right_contact_original_primitives"]
        for sign in (1, -1):
            for primitive in [*primitives["base_tabs"], primitives["under_cell_base"]]:
                xs = sorted(100 + sign * primitive[k] for k in ("x_min", "x_max"))
                bounds = [xs[0], 100-primitive["y_width"]/2, xs[1], 100+primitive["y_width"]/2]
                shape = bounds_polygon(pcb, {"bounds_absolute_iu": [pcb.FromMM(v) for v in bounds]})
                self.metal.append((shape, bounds))

    def masks(self, net, width, xs, ys, allow_vias):
        pcb = self.pcb
        masks = np.zeros((2, len(ys), len(xs)), dtype=bool)
        via_mask = np.zeros((len(ys), len(xs)), dtype=bool)
        # Existing MCU escapes use the exact clearance floor. Check full edges
        # after searching instead of inflating away those usable corridors.
        guard = -.000001

        def mark(mask, shape, bounds, radius, clearance):
            margin = radius + clearance
            lo_x, lo_y, hi_x, hi_y = bounds
            i0 = max(0, math.floor((lo_x-100-margin-xs[0])/GRID))
            i1 = min(len(xs), math.ceil((hi_x-100+margin-xs[0])/GRID)+1)
            j0 = max(0, math.floor((lo_y-100-margin-ys[0])/GRID))
            j1 = min(len(ys), math.ceil((hi_y-100+margin-ys[0])/GRID)+1)
            for j in range(j0, j1):
                for i in range(i0, i1):
                    if mask[j, i]:
                        continue
                    circle = pcb.SHAPE_CIRCLE(
                        pcb.VECTOR2I(pcb.FromMM(float(xs[i]+100)), pcb.FromMM(float(ys[j]+100))),
                        pcb.FromMM(radius))
                    if shape.Collide(circle, pcb.FromMM(clearance)):
                        mask[j, i] = True
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
